mike42/65816-computer/emulator/src/cpu/opcodes/OpCode_CPX_CPY.cpp

/*
 * This file is part of the 65816 Emulator Library.
 * Copyright (c) 2018 Francesco Rigoni.
 *
 * https://github.com/FrancescoRigoni/Lib65816
 *
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
 * You should have received a copy of the GNU General Public License
 * along with this program. If not, see <http://www.gnu.org/licenses/>.
 */

#include "Cpu65816.h"

#define LOG_TAG "Cpu::executeCPXCPY"

/**
 * This file contains implementations for all CPX and CPY OpCodes.
 */

void Cpu65816::execute8BitCPX(OpCode &opCode) {
    uint8_t value = mSystemBus.readByte(getAddressOfOpCodeData(opCode));
    uint8_t result = Binary::lower8BitsOf(mX) - value;
    mCpuStatus.updateSignAndZeroFlagFrom8BitValue(result);
    if (Binary::lower8BitsOf(mX) >= value) mCpuStatus.setCarryFlag();
    else mCpuStatus.clearCarryFlag();
}

void Cpu65816::execute16BitCPX(OpCode &opCode) {
    uint16_t value = mSystemBus.readTwoBytes(getAddressOfOpCodeData(opCode));
    uint16_t result = mX - value;
    mCpuStatus.updateSignAndZeroFlagFrom16BitValue(result);
    if (mX >= value) mCpuStatus.setCarryFlag();
    else mCpuStatus.clearCarryFlag();
}

void Cpu65816::execute8BitCPY(OpCode &opCode) {
    uint8_t value = mSystemBus.readByte(getAddressOfOpCodeData(opCode));
    uint8_t result = Binary::lower8BitsOf(mY) - value;
    mCpuStatus.updateSignAndZeroFlagFrom8BitValue(result);
    if (Binary::lower8BitsOf(mY) >= value) mCpuStatus.setCarryFlag();
    else mCpuStatus.clearCarryFlag();
}

void Cpu65816::execute16BitCPY(OpCode &opCode) {
    uint16_t value = mSystemBus.readTwoBytes(getAddressOfOpCodeData(opCode));
    uint16_t result = mY - value;
    mCpuStatus.updateSignAndZeroFlagFrom16BitValue(result);
    if (mY >= value) mCpuStatus.setCarryFlag();
    else mCpuStatus.clearCarryFlag();
}

void Cpu65816::executeCPXCPY(OpCode &opCode) {
    switch (opCode.getCode()) {
        case (0xE0):  // CPX Immediate
        {
            if (indexIs8BitWide()) {
                execute8BitCPX(opCode);
            } else {
                execute16BitCPX(opCode);
                addToProgramAddress(1);
                addToCycles(1);
            }
            addToProgramAddressAndCycles(2, 2);
            break;
        }
        case (0xEC):  // CPX Absolute
        {
            if (indexIs8BitWide()) {
                execute8BitCPX(opCode);
            } else {
                execute16BitCPX(opCode);
                addToCycles(1);
            }
            addToProgramAddressAndCycles(3, 4);
            break;
        }
        case (0xE4):  // CPX Direct Page
        {
            if (indexIs8BitWide()) {
                execute8BitCPX(opCode);
            } else {
                execute16BitCPX(opCode);
                addToCycles(1);
            }
            if (Binary::lower8BitsOf(mD) != 0) {
                addToCycles(1);
            }
            addToProgramAddressAndCycles(2, 3);
            break;
        }
        case (0xC0):  // CPY Immediate
        {
            if (indexIs8BitWide()) {
                execute8BitCPY(opCode);
            } else {
                execute16BitCPY(opCode);
                addToProgramAddress(1);
                addToCycles(1);
            }
            addToProgramAddressAndCycles(2, 2);
            break;
        }
        case (0xCC):  // CPY Absolute
        {
            if (indexIs8BitWide()) {
                execute8BitCPY(opCode);
            } else {
                execute16BitCPY(opCode);
                addToCycles(1);
            }
            addToProgramAddressAndCycles(3, 4);
            break;
        }
        case (0xC4):  // CPY Direct Page
        {
            if (indexIs8BitWide()) {
                execute8BitCPY(opCode);
            } else {
                execute16BitCPY(opCode);
                addToCycles(1);
            }
            if (Binary::lower8BitsOf(mD) != 0) {
                addToCycles(1);
            }
            addToProgramAddressAndCycles(2, 3);
            break;
        }
        default: {
            LOG_UNEXPECTED_OPCODE(opCode);
        }
    }
}
