mike42/65816-computer/emulator/src/cpu/opcodes/OpCode_TSB_TRB.cpp

/*
 * This file is part of the 65816 Emulator Library.
 * Copyright (c) 2018 Francesco Rigoni.
 *
 * https://github.com/FrancescoRigoni/Lib65816
 *
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
 * You should have received a copy of the GNU General Public License
 * along with this program. If not, see <http://www.gnu.org/licenses/>.
 */

#include "Interrupt.h"
#include "Cpu65816.h"

#define LOG_TAG "Cpu::executeTSBTRB"

/**
 * This file contains the implementation for TSB and TRB OpCodes
 */

void Cpu65816::execute8BitTSB(OpCode &opCode) {
    const Address addressOfOpCodeData = getAddressOfOpCodeData(opCode);
    uint8_t value = mSystemBus.readByte(addressOfOpCodeData);
    uint8_t lowerA = Binary::lower8BitsOf(mA);
    const uint8_t result = value | lowerA;
    mSystemBus.storeByte(addressOfOpCodeData, result);

    if ((value & lowerA) == 0) mCpuStatus.setZeroFlag();
    else mCpuStatus.clearZeroFlag();
}

void Cpu65816::execute16BitTSB(OpCode &opCode) {
    const Address addressOfOpCodeData = getAddressOfOpCodeData(opCode);
    uint16_t value = mSystemBus.readTwoBytes(addressOfOpCodeData);
    const uint16_t result = value | mA;
    mSystemBus.storeTwoBytes(addressOfOpCodeData, result);

    if ((value & mA) == 0) mCpuStatus.setZeroFlag();
    else mCpuStatus.clearZeroFlag();
}

void Cpu65816::execute8BitTRB(OpCode &opCode) {
    const Address addressOfOpCodeData = getAddressOfOpCodeData(opCode);
    uint8_t value = mSystemBus.readByte(addressOfOpCodeData);
    uint8_t lowerA = Binary::lower8BitsOf(mA);
    const uint8_t result = value & ~lowerA;
    mSystemBus.storeByte(addressOfOpCodeData, result);

    if ((value & lowerA) == 0) mCpuStatus.setZeroFlag();
    else mCpuStatus.clearZeroFlag();
}

void Cpu65816::execute16BitTRB(OpCode &opCode) {
    const Address addressOfOpCodeData = getAddressOfOpCodeData(opCode);
    uint16_t value = mSystemBus.readTwoBytes(addressOfOpCodeData);
    const uint16_t result = value & ~mA;
    mSystemBus.storeTwoBytes(addressOfOpCodeData, result);

    if ((value & mA) == 0) mCpuStatus.setZeroFlag();
    else mCpuStatus.clearZeroFlag();
}

void Cpu65816::executeTSBTRB(OpCode &opCode) {
    switch (opCode.getCode()) {
        case (0x0C):                 // TSB Absolute
        {
            if (accumulatorIs8BitWide()) {
                execute8BitTSB(opCode);
            } else {
                execute16BitTSB(opCode);
                addToCycles(2);
            }
            addToProgramAddressAndCycles(3, 6);
            break;
        }
        case (0x04):                 // TSB Direct Page
        {
            if (accumulatorIs8BitWide()) {
                execute8BitTSB(opCode);
            } else {
                execute16BitTSB(opCode);
                addToCycles(2);
            }
            if (Binary::lower8BitsOf(mD) != 0) {
                addToCycles(1);
            }
            addToProgramAddressAndCycles(2, 5);
            break;
        }
        case (0x1C):                 // TRB Absolute
        {
            if (accumulatorIs8BitWide()) {
                execute8BitTRB(opCode);
            } else {
                execute16BitTRB(opCode);
                addToCycles(2);
            }
            addToProgramAddressAndCycles(3, 6);
            break;
        }
        case (0x14):                 // TRB Direct Page
        {
            if (accumulatorIs8BitWide()) {
                execute8BitTRB(opCode);
            } else {
                execute16BitTRB(opCode);
                addToCycles(2);
            }
            if (Binary::lower8BitsOf(mD) != 0) {
                addToCycles(1);
            }
            addToProgramAddressAndCycles(2, 5);
            break;
        }
        default: {
            LOG_UNEXPECTED_OPCODE(opCode);
        }
    }
}
